HarveyBates/esp32-clover/electronics/esp32-clover/components/extern/tmp/ZXMP7A17KTC/TO-252-3_6P6X6P1_DIO.step

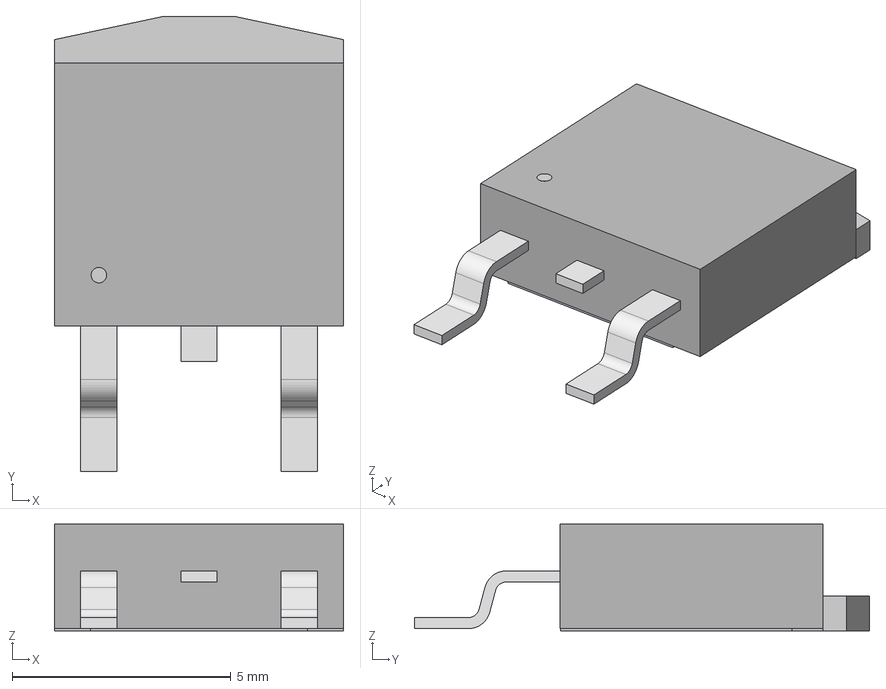
[picture p17: CAD file, 2023-08-07]
electronics/esp32-clover/components/extern/tmp/ZXMP7A17KTC/TO-252-3_6P6X6P1_DIO.step
6.60 x 10.4 x 2.44 mm
